dojoe/Twonkie/ref/twinkie/180-10114-04_fab/180-10114-04_fab.pdf

ART FILM - fab

ART FILM - fab

# BDCA

04

REV
180-10114

11

DWG NO

# TWINKIE

# FAB DRAWING D

SIZE

TOTAL: .6MM +/- 10%

* SURFACE - AIR 0 MM
L1: TOP CONDUCTOR - COPPER 0.0356 MM

* DIELECTRIC - FR-4 0.1 MM

L2: GND1 PLANE - COPPER 0.0178 MM

* DIELECTRIC - FR-4 0.0762 MM

L3: SIGNAL_1 CONDUCTOR - COPPER 0.0178 MM

* DIELECTRIC - FR-4 0.1 MM

L4: SIGNAL_2 CONDUCTOR - COPPER 0.0178 MM

* DIELECTRIC - FR-4 0.0762 MM

L5: PWR1 PLANE - COPPER 0.0178 MM

* DIELECTRIC - FR-4 0.1 MM

L6: BOTTOM CONDUCTOR - COPPER 0.0356 MM * SURFACE - AIR 0 MM

o

UNLESS OTHERWISE SPECIFIED

DIMENSIONS ARE IN METRIC
TOLERANCES ON:
DIMENSIONS +/- .05

# ANGLES +/- 5 22

5-6

4-5

3-4

2-3

1-2

16.25

1-6

9.5

33

4.455

plated 118 - 250 microinches Immersion Gold (ENIG).

9.105

21.611 44

7.9

2.106

1.281
1.563

1.55

1.281

of Electroless Nickel and 2 - 8 | microinches of
after ENIG | process.
with IPC-SM-840, Type B, Class 2, over bare copper. Soldermask color | to | be White.

Lands and exposed plated areas to be free of ink.

a. Glass epoxy, natural color, laminated polyclad 370hr. Tg of 170C minimum. The final thickness measured over plating to be 0.60 MM, +/- 10%.
a. All external metal finish not covered by soldermask shall be
a. All non test point top side vias to be encroached (hole size +5 mils) with soldermask.
b. All non test point bottom side vias to be encroached (hole size +5 mils) and post plug
c. All vias to be plugged.
d. All BGA vias and test points vias are to be free of soldermask.
e. Tangency is allowed on vias provided tear dropping is applied to the entry of the trace to the pad. All other plated holes shall have a minimum annular ring of .001".
a. All hole symbols may not be shown in the drawing. See Drill chart for details.
b. Diameters in the drill table are finished hole sizes with +/-0.003" tolerance unless otherwise specified in the drill table.
a. Soldermask,photo-imaged liquid polymer on both sides of boards in accordance
b. Component Marking: Silkscreen Bottom side with black, non-conductive epoxy ink.

1.225

3. Material:
4. Surface Finish:
5. Via:
6. Drilling:
7. Marking:

5⁶.35

5

7.05

1.225

2.85

97122421

### QTY

221

### QTY

176

### QTY

159

### QTY

110

### QTY

### QTY

### PLATED PLATED

### PLATED PLATED

### PLATED

# PLATED 6

### PLATED PLATED

### PLATED PLATED

### PLATED

### PLATED PLATED PLATED PLATED

### NON-PLATED

# NON-PLATED 6

### TOLERANCE

### TOLERANCE

### TOLERANCE

### TOLERANCE

### TOLERANCE

### TOLERANCE

+0.1/-0.1

+0.1/-0.1
+0.1/-0.1

+0.076/-0.1

+0.076/-0.1

+0.076/-0.1

+0.0762/-0.1

+0.0762/-0.1

+0.076/-0.076
+0.076/-0.076

+0.076/-0.076

### DRILL CHART: TOP to GND1

### DRILL CHART: PWR1 to BOTTOM

### DRILL CHART: TOP to BOTTOM

### ALL UNITS ARE IN MILLIMETERS

0.1

### ALL UNITS ARE IN MILLIMETERS

0.1

### ALL UNITS ARE IN MILLIMETERS SIZE

0.1

### ALL UNITS ARE IN MILLIMETERS SIZE

0.1

### ALL UNITS ARE IN MILLIMETERS SIZE

0.1

### ALL UNITS ARE IN MILLIMETERS

### SIZE

### DRILL CHART: GND1 to SIGNAL_1

### SIZE

### DRILL CHART: SIGNAL_2 to PWR1

### SIZE

0.65

### DRILL CHART: SIGNAL_1 to SIGNAL_2

1.1x0.5
1.3x0.6
1.5x0.5
1.6x0.6
0.95x0.65

and IPC 9252 class II. Completed electrical test Boards must be marked in permanent non-conductive ink next to supplier UL recognition mark.

drawing shall be controlled by the gerber data.

than the smaller of .001" or 20% of the trace width from the gerber data.

# away from any designed features (i.e. vias, pads, traces, etc.). 7

Substances (RoHS) Directive and compatible with Pb Free assembly process.

a. Board shall be built per IPC-A-600 and IPC-6012, class II, latest revision.
c. Configuration of the printed circuit board not specifically dimensioned on the
d. Bow and Twist: shall not exceed .007" per inch.

a .157 traces on top and bottom to be 85ohm +/- 10%
b. .1016mm traces on internal layers 3 and 4 to be 85ohm +/- 10% b. Board shall be electrically tested per current revision of IPC 6012
e. Fabrication Tolerances: end product trace widths and lands shall not vary more
f. PCB fabrication process and materials must be compliant with the Hazadous
g. Theiving is allowed on all layers with 0.050" squares on 0.100" pitch and 0.100" min 7
1. General Requirement:
2. Impedance Control:

### FIGURE

### FIGURE

### FIGURE

### FIGURE

### FIGURE

### FIGURE

NOTES: Unless otherwise specified

DCBA
