dojoe/Twonkie/pic/twonkie-v0.99-back.jpg

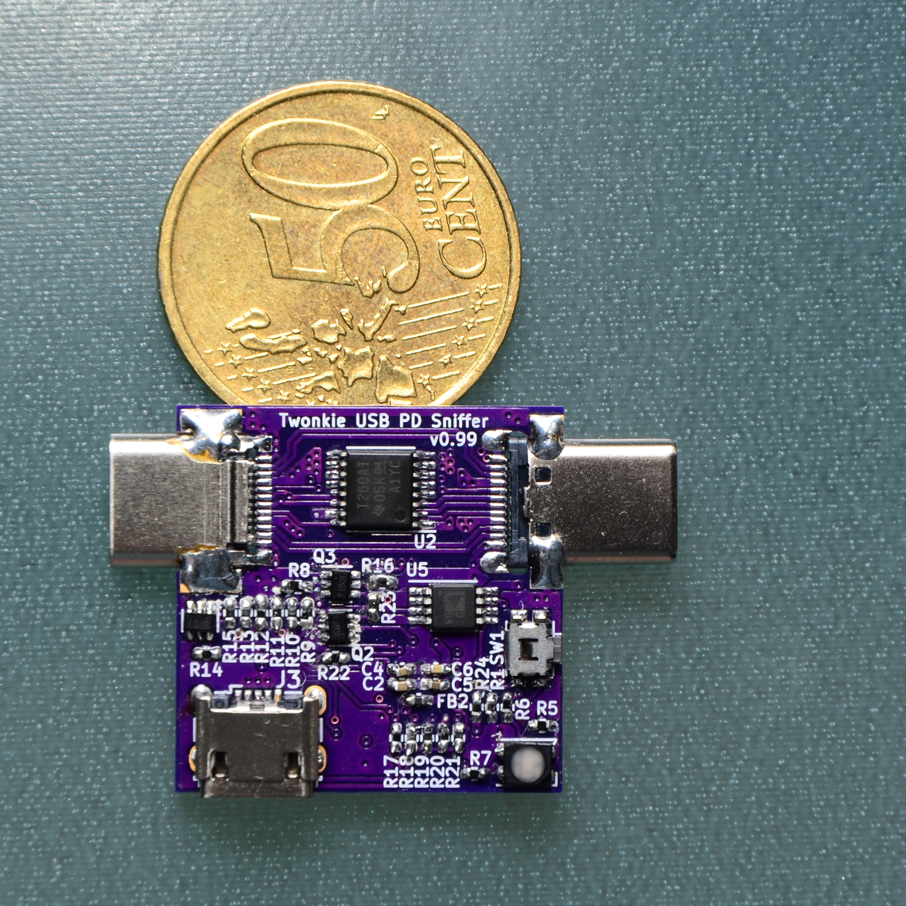
pic/twonkie-v0.99-back.jpg
