dojoe/Twonkie/pic/twonkie-v0.99-front.jpg

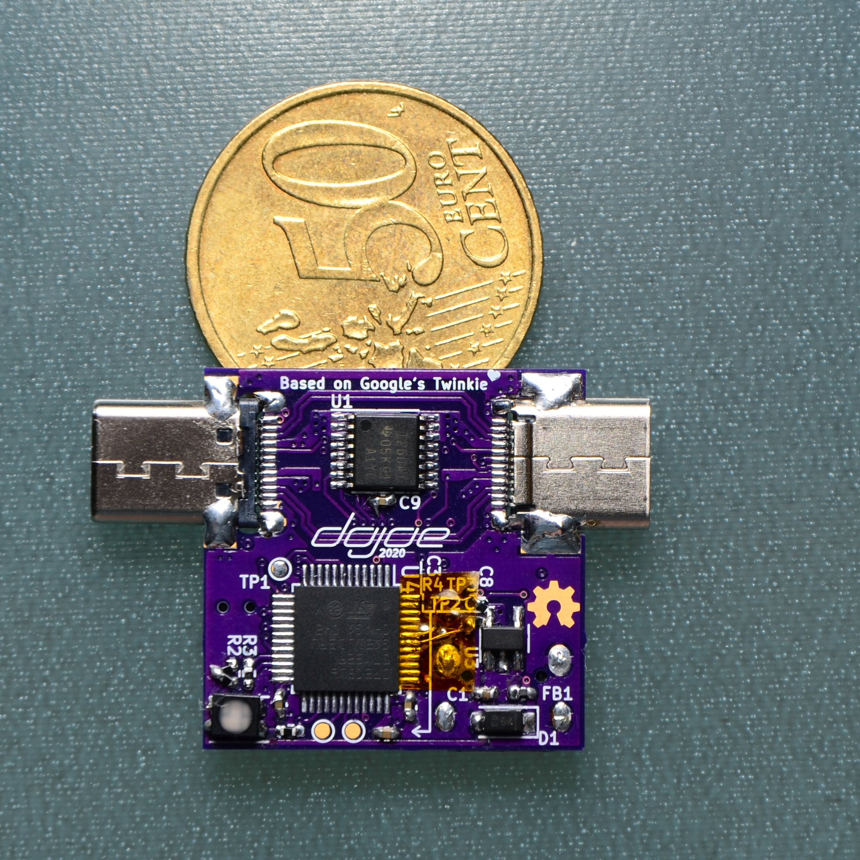
pic/twonkie-v0.99-front.jpg
