dojoe/Twonkie/pic/twonkie-v0.99.jpg

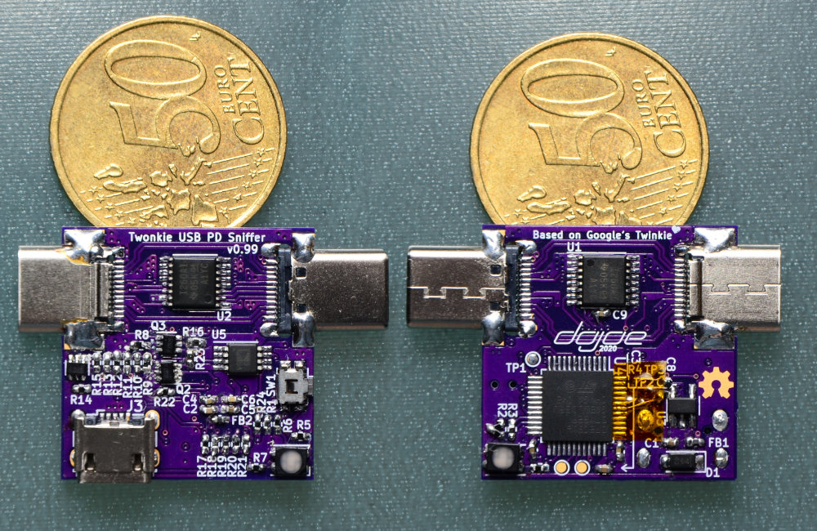
pic/twonkie-v0.99.jpg
