dojoe/Twonkie/ref/twinkie/Housing_bottom_inside.png

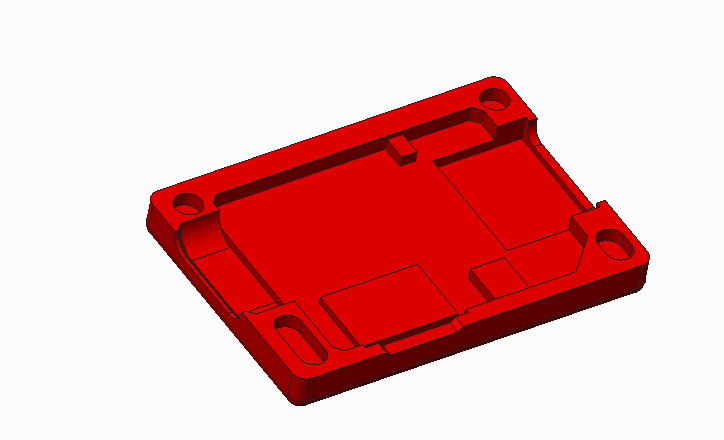
ref/twinkie/Housing_bottom_inside.png
