dojoe/Twonkie/ref/twinkie/Housing_bottom_outside.png

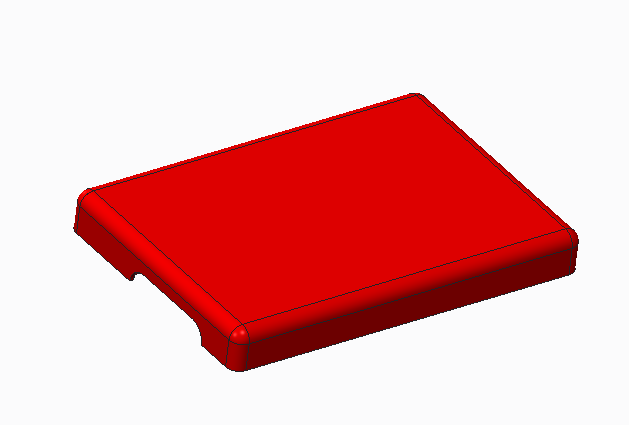
ref/twinkie/Housing_bottom_outside.png
