dojoe/Twonkie/ref/twinkie/Housing_top_inside.png

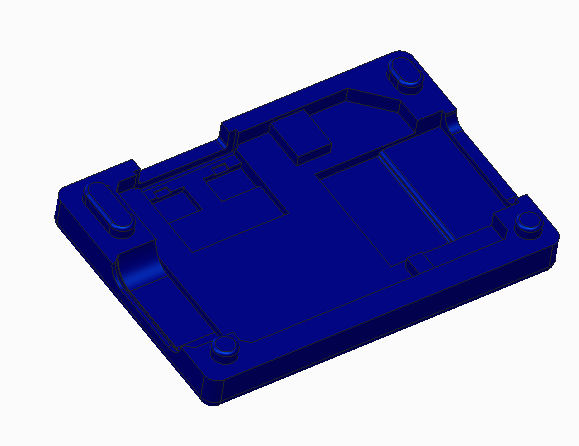
ref/twinkie/Housing_top_inside.png
