dojoe/Twonkie/ref/twinkie/Housing_top_outside.png

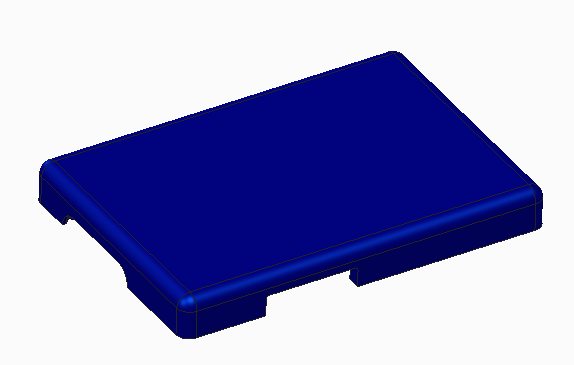
ref/twinkie/Housing_top_outside.png
