dojoe/Twonkie/hw/v2.0/twonkie.pdf

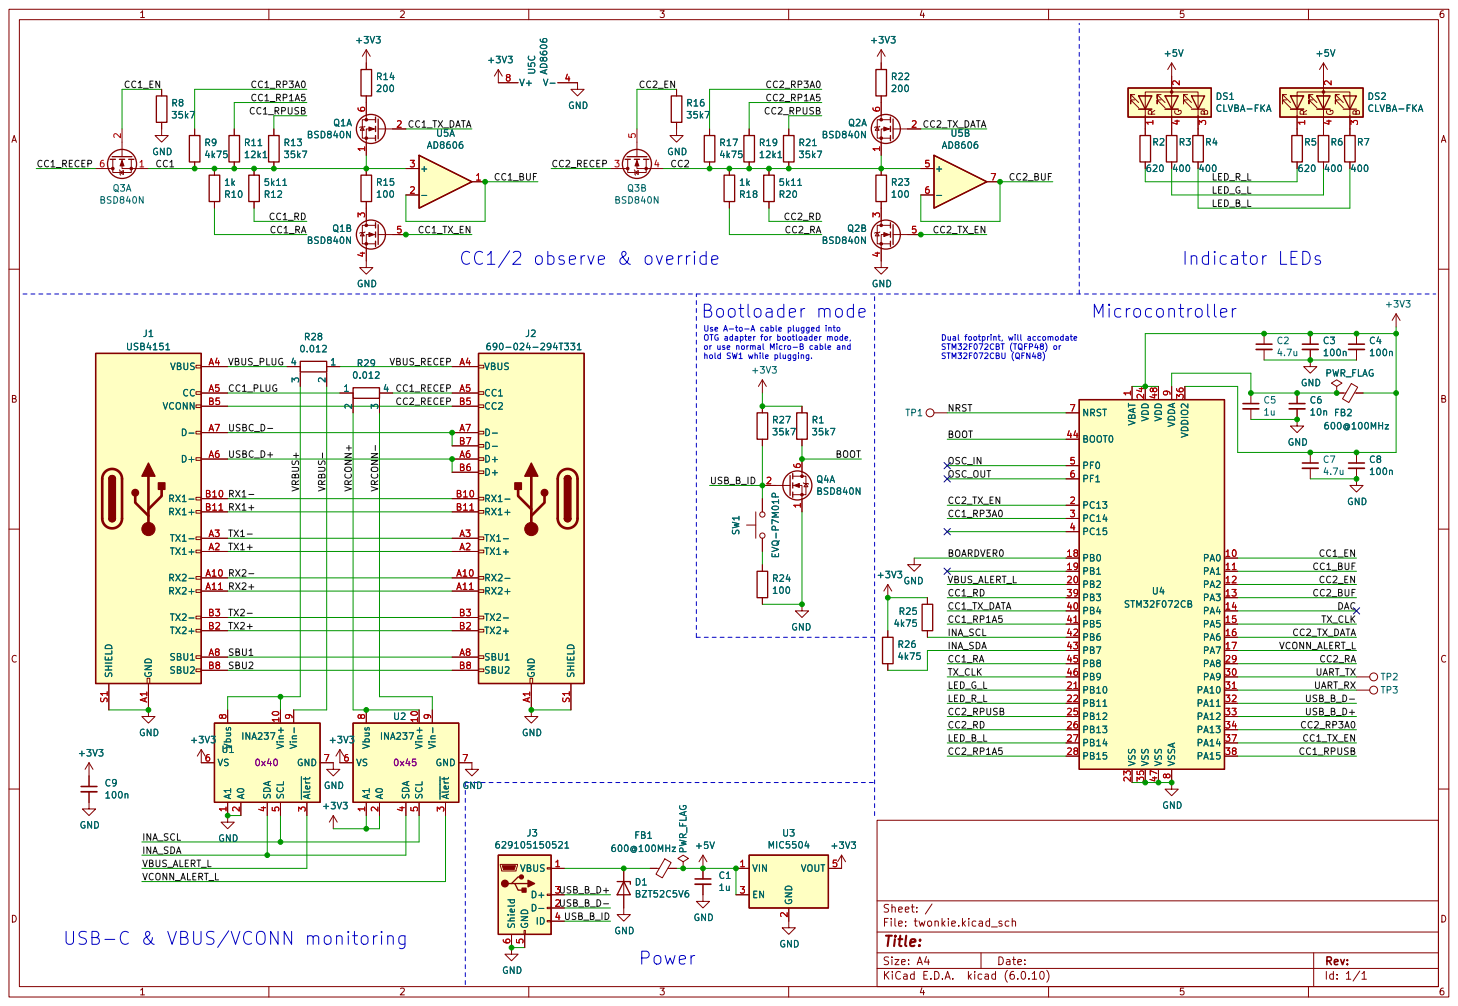
[picture p30: page 1]

hold SW1 while plugging. CC1/2 observe & override

Dual footprint, will accomodate STM32F072CBT (TQFP48) or STM32F072CBU (QFN48) Use A-to-A cable plugged into OTG adapter for bootloader mode, or use normal Micro-B cable and

1 PA0 10 PA1 11 PA2 12 PA3 13 PA4 14 PA5 15 PA6 16 PA7 17 PB0 18 PB1 19 PC13 2 PB2 20 PB10 21 PB11 22 VSS 23 VDD 24 PB12 25 PB13 26 PB14 27 PB15 28 PA8 29 PC14 3 PA9 30 PA10 31 PA11 32 PA12 33 PA13 34 VSS 35 VDDIO2 36 PA14 37 PA15 38 PB3 39 PC15 4 PB4 40 PB5 41 PB6 42 PB7 43 BOOT0 44 PB8 45 PB9 46 VSS 47 VDD 48 PF0 5 PF1 6 NRST 7 VSSA
LED_G_L OSC_IN OSC_OUT BOOT VBUS_ALERT_L CC1_TX_DATA CC1_RD

5 VS 6 GND 7 Vbus 8 Vin- U2 9

5 VS 6 GND 7 Vbus 8 Vin- 9 +3V3

5 VS 6 GND 7 Vbus 8 Vin- 9 U1

5 VS 6 GND 7 Vbus 8 Vin- 9 GND

2 EN 3 VOUT 5 GND GND

USB-C & VBUS/VCONN monitoring
