dojoe/Twonkie/ref/twinkie/810-10114-04_sch.pdf

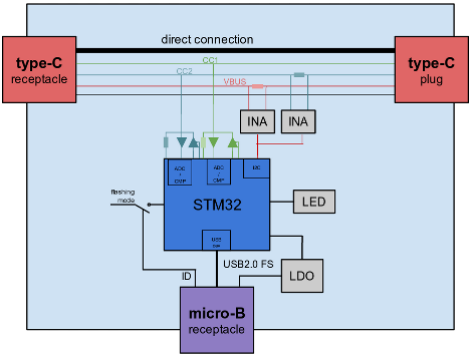
[picture p31: figure]

Thu Jan 8 13:33:56 2015 | 1 OF 2

# Twinkie USB PD debugger

# SCH: 810-10114-04 ASSY:803-10114-04 PCB: 180-10114-04

1 | TABLE OF CONTENTS
2 | TWINKIE
twinkie | 810-10114-04 | 0.00

# TABLE OF CONTENTS

SHEET NO. | SHEET NAME

## TABLE OF CONTENTS

DESIGN:

TITLE:

PAGE

13

DOC NUMBER:

FLAT:
16

17

17

9

L

K | K
J | J

H

G

F

E | E
D | D
C | C
B | B

A

L

G

F

1 | 2 | 3 | 5 | 6 | 7 | 8 | 10 | 11 | 12 | 13 | 14 | 16
4 | 5 | 6 | 7 | 8 | 9

4

2

3 | 14 | 15

PAGE:

REV:
MODIFIED:
1 | 10 | 11

A

H

12

THESE MATERIALS (INCLUDING ALL TEXT, SOFTWARE, CODE, DISPLAYS, ARTWORK, AND IMAGES) ARE LICENSED UNDER A CREATIVE COMMONS ATTRIBUTION 2.5 LICENSE.

15

### B=3.0MA@3.2VF

### G=3.0MA@3.3VF

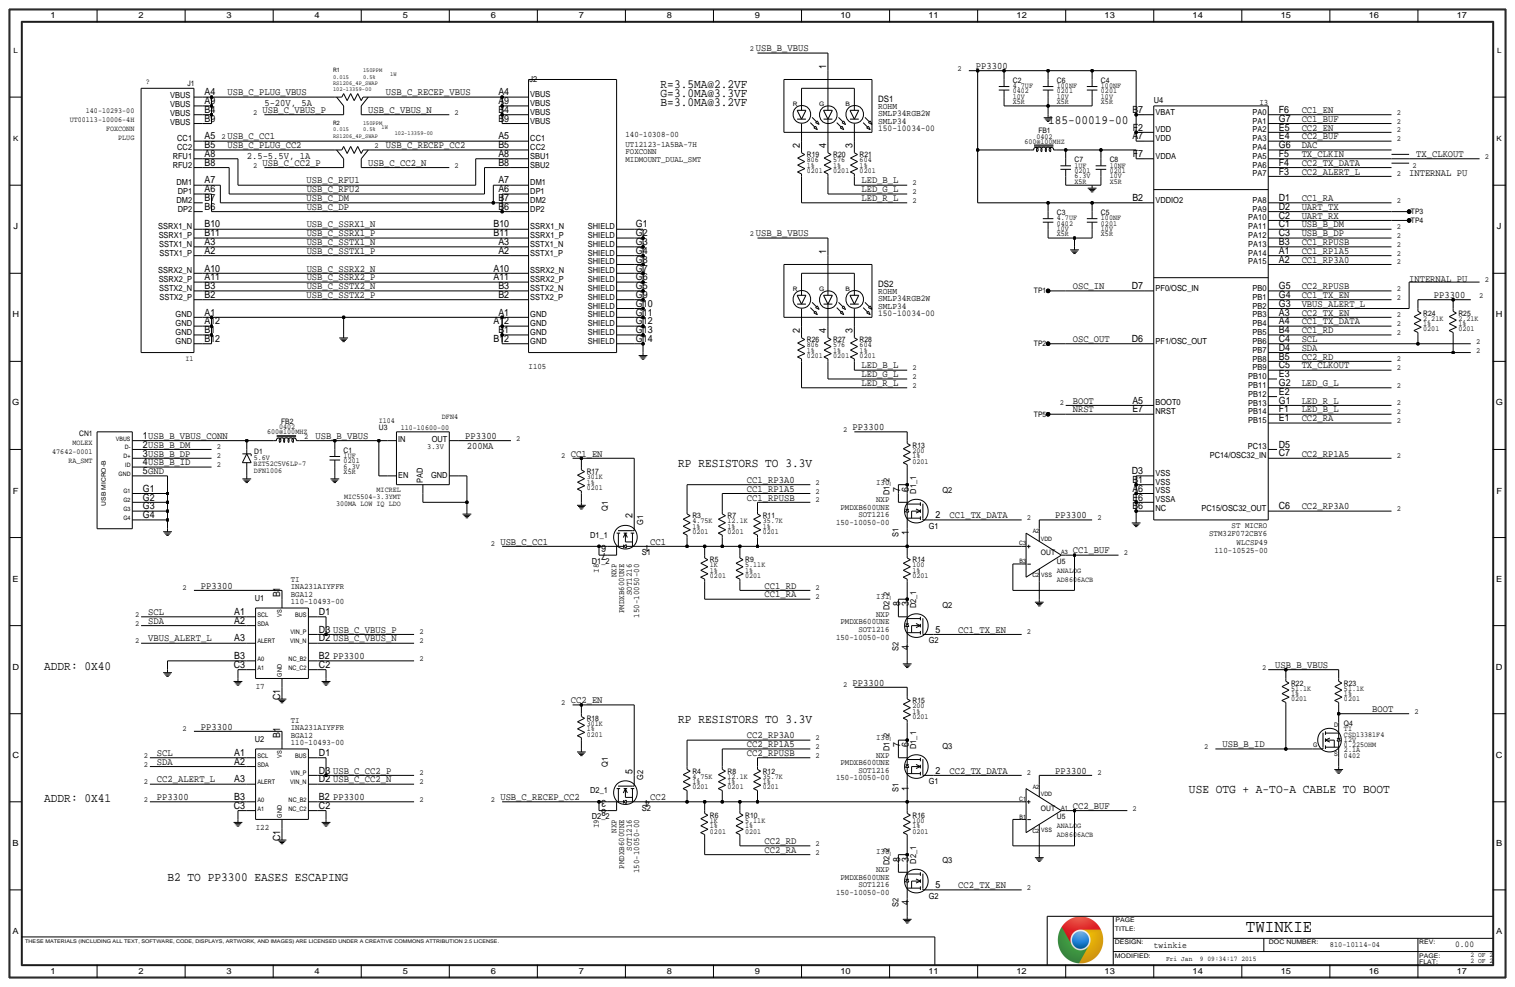
[picture p32: page 2]

B11 USB_C_SSRX1_P B11 | G2
A3 USB_C_SSTX1_N A3 | G3
A2 USB_C_SSTX1_P A2 | G4
A10 USB_C_SSRX2_N A10 | G8

B1 | | B1
B12 | B12

USB_B_ID
USE OTG + A-TO-A CABLE TO BOOT

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
