dojoe/Twonkie/ref/twinkie/180-10114-04_assy/180-10114-04_assy.pdf

# BDCA

11

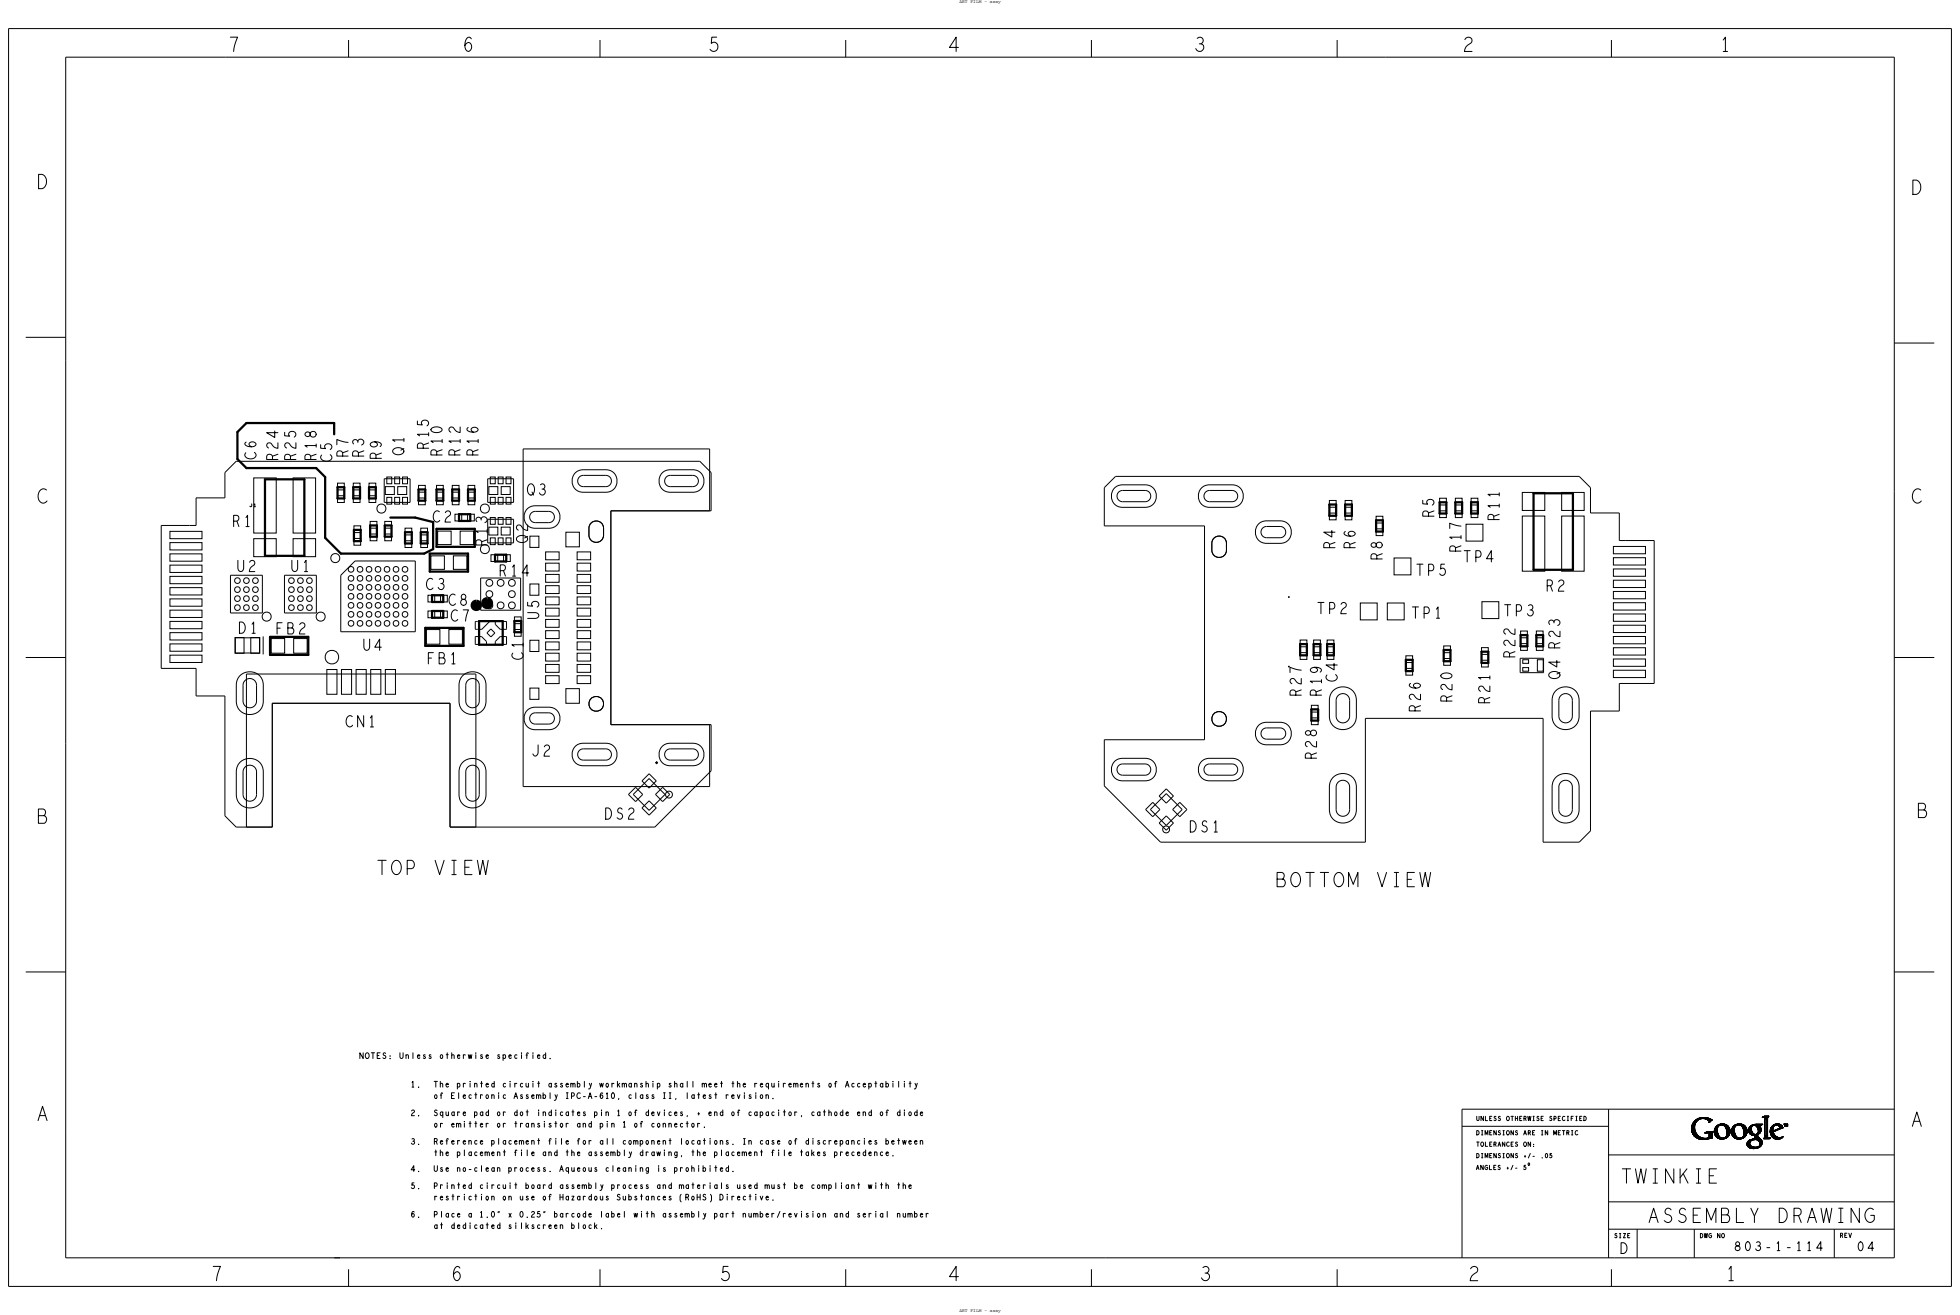
[picture p33: page 1]

DCBA
NOTES: Unless otherwise specified. R3
TOP VIEW R9

DIMENSIONS ARE IN METRIC
TOLERANCES ON:
DIMENSIONS +/- .05

ASSEMBLY DRAWING
SIZE | DWG NO 803-1-114 | REV 04
