dojoe/Twonkie/hw/v0.99/schematics.pdf

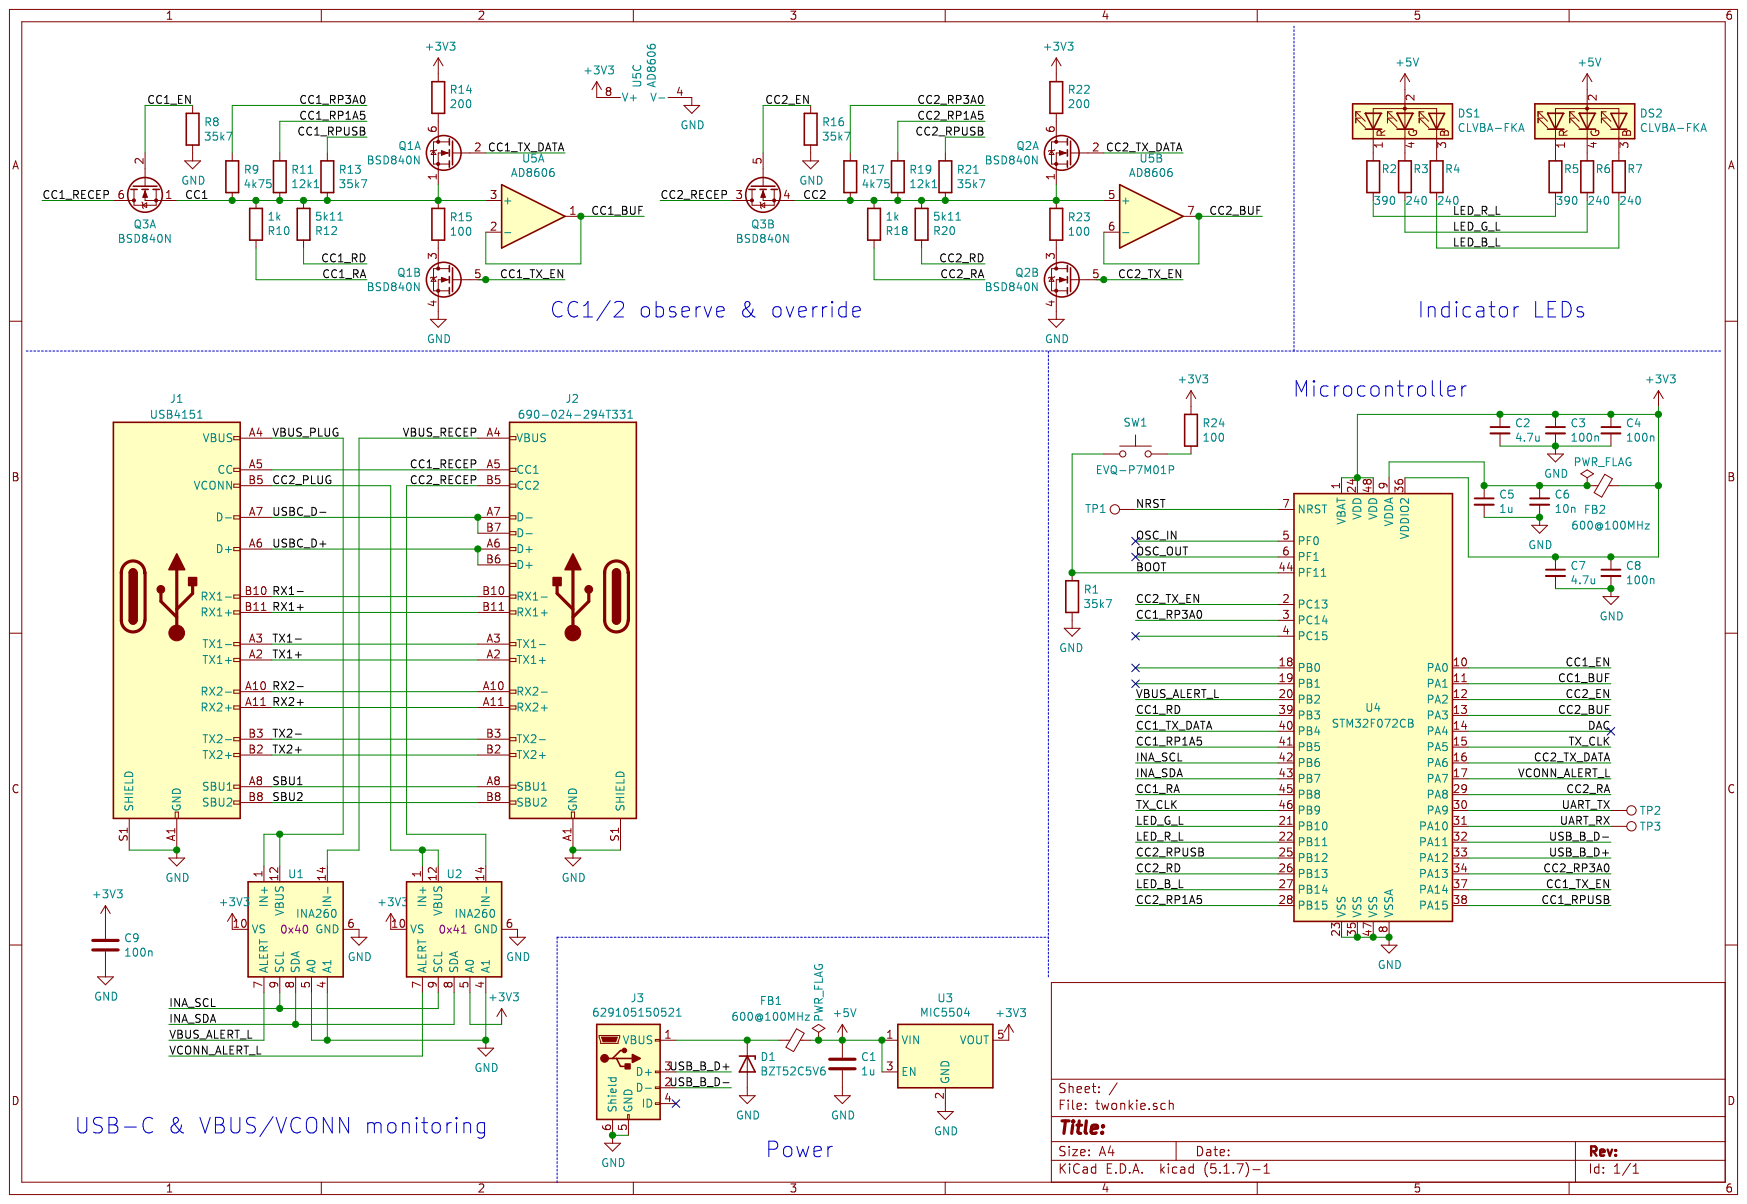
[picture p34: page 1]
