dojoe/Twonkie/fw/board/twinkie/board.c

/* Copyright (c) 2014 The Chromium OS Authors. All rights reserved.
 * Use of this source code is governed by a BSD-style license that can be
 * found in the LICENSE file.
 */
/* Twinkie dongle configuration */

#include "adc.h"
#include "adc_chip.h"
#include "common.h"
#include "console.h"
#include "ec_version.h"
#include "gpio.h"
#include "hooks.h"
#include "i2c.h"
#include "ina2xx.h"
#include "printf.h"
#include "registers.h"
#include "system.h"
#include "task.h"
#include "usb_descriptor.h"
#include "util.h"

void cc2_event(enum gpio_signal signal)
{
	ccprintf("INA!\n");
}

void vbus_event(enum gpio_signal signal)
{
	ccprintf("INA!\n");
}

#include "gpio_list.h"

/* Initialize board. */
void board_config_pre_init(void)
{
	/* enable SYSCFG clock */
	STM32_RCC_APB2ENR |= 1 << 0;
	/* Remap USART DMA to match the USART driver and TIM2 DMA */
	STM32_SYSCFG_CFGR1 |= (1 << 9) | (1 << 10) /* Remap USART1 RX/TX DMA */
			   |  (1 << 29);/* Remap TIM2 DMA */
	/* 40 MHz pin speed on UART PA9/PA10 */
	STM32_GPIO_OSPEEDR(GPIO_A) |= 0x003C0000;
	/* 40 MHz pin speed on TX clock out PB9 */
	STM32_GPIO_OSPEEDR(GPIO_B) |= 0x000C0000;
}

static void board_init(void)
{
	const uint16_t calib = INA2XX_CALIB_1MA(INA_SENSE_MOHMS);
	const uint32_t vbus_mode =
		INA2XX_CONFIG_BUS_CONV_TIME(INA2XX_CONV_TIME_1100) |
		INA2XX_CONFIG_SHUNT_CONV_TIME(INA2XX_CONV_TIME_1100) |
		INA2XX_CONFIG_MODE_BUS | INA2XX_CONFIG_MODE_SHUNT |
		INA2XX_CONFIG_MODE_CONT;
	const uint32_t vconn_mode =
		INA2XX_CONFIG_BUS_CONV_TIME(INA2XX_CONV_TIME_1100) |
		INA2XX_CONFIG_SHUNT_CONV_TIME(INA2XX_CONV_TIME_1100) |
		INA2XX_CONFIG_MODE_BUS | INA2XX_CONFIG_MODE_SHUNT |
		/* Disable INA1 (VCONN2) to avoid leaking current */
		INA2XX_CONFIG_MODE_TRG;

#ifdef BOARD_TWONKIEV2
	// INA1 address tied to 5 instead of 1 for easier board routing :/
	ina2xx_addresses[1] = INA2XX_I2C_ADDR(5);
#endif

	/* Enable interrupts for INAs. */
	gpio_enable_interrupt(GPIO_CC2_ALERT_L);
	gpio_enable_interrupt(GPIO_VBUS_ALERT_L);

	ina2xx_init(0, vbus_mode, calib);
	ina2xx_init(1, vconn_mode, calib);
}
DECLARE_HOOK(HOOK_INIT, board_init, HOOK_PRIO_DEFAULT);

/* ADC channels */
const struct adc_t adc_channels[] = {
	/* USB PD CC lines sensing. Converted to mV (3300mV/4096). */
	[ADC_CH_CC1_PD] = {"CC1_PD", 3300, 4096, 0, STM32_AIN(1)},
	[ADC_CH_CC2_PD] = {"CC2_PD", 3300, 4096, 0, STM32_AIN(3)},
};
BUILD_ASSERT(ARRAY_SIZE(adc_channels) == ADC_CH_COUNT);

/* I2C ports */
const struct i2c_port_t i2c_ports[] = {
	{"master", I2C_PORT_MASTER, 100, GPIO_I2C_SCL, GPIO_I2C_SDA},
};
const unsigned int i2c_ports_used = ARRAY_SIZE(i2c_ports);

const void * const usb_strings[] = {
	[USB_STR_DESC] = usb_string_desc,
	[USB_STR_VENDOR] = USB_STRING_DESC("Google Inc."),
	[USB_STR_PRODUCT] = USB_STRING_DESC("Twinkie"),
	[USB_STR_VERSION] = USB_STRING_DESC(CROS_EC_VERSION32),
	[USB_STR_SNIFFER] = USB_STRING_DESC("USB-PD Sniffer"),
	[USB_STR_CONSOLE_NAME] = USB_STRING_DESC("Shell"),
	[USB_STR_COMMAND_NAME] = USB_STRING_DESC("Commands"),
	[USB_STR_SERIALNO] = USB_STRING_DESC(""),
};
BUILD_ASSERT(ARRAY_SIZE(usb_strings) == USB_STR_COUNT);

/* Generate a USB serial number from unique chip ID. */
const char *board_read_serial(void)
{
	static char str[USB_STRING_LEN];

	if (str[0] == '\0') {
		uint8_t *id;
		int pos = 0;
		int idlen = system_get_chip_unique_id(&id);
		int i;

		for (i = 0; i < idlen && pos < sizeof(str); i++, pos += 2)
			snprintf(&str[pos], sizeof(str)-pos, "%02x", id[i]);
	}

	return str;
}
